OrsoEric/18650-Battery-Holder/Images/2024-06-14_17_49_IMG_20240614_174955.jpg

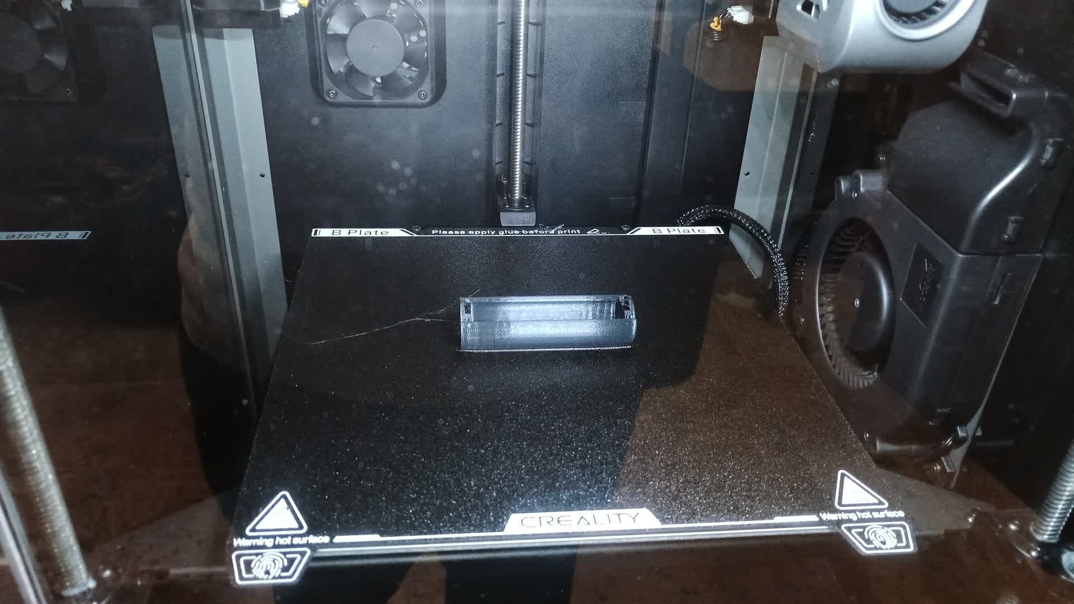
Images/2024-06-14_17_49_IMG_20240614_174955.jpg
