OrsoEric/18650-Battery-Holder/Images/2024-06-14_17_50_IMG_20240614_175002.jpg

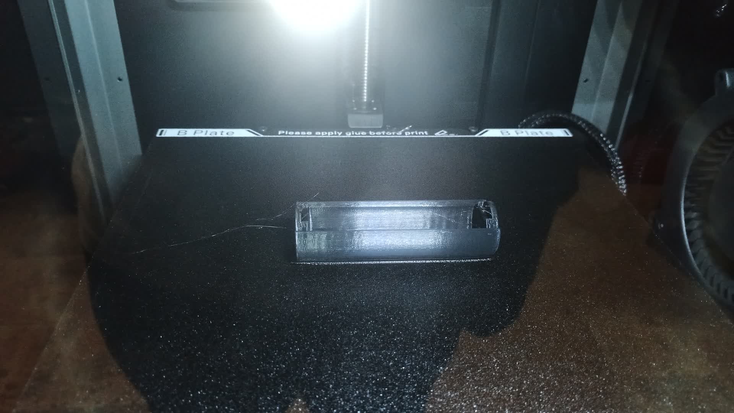
Images/2024-06-14_17_50_IMG_20240614_175002.jpg
