OrsoEric/18650-Battery-Holder/Images/2024-06-23_15_02_IMG_20240623_150227.jpg

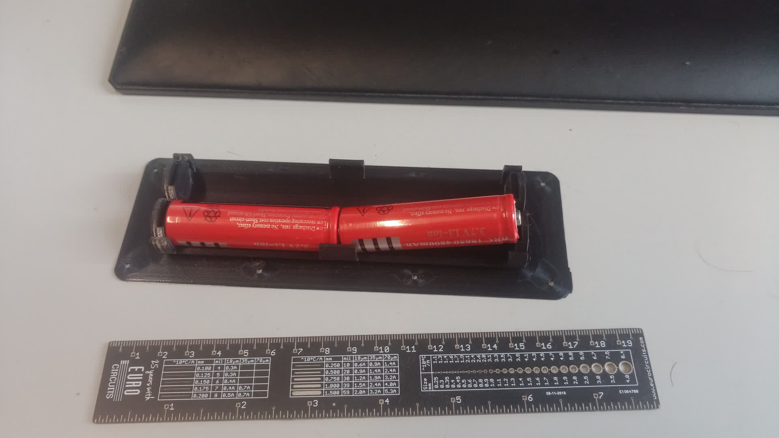
Images/2024-06-23_15_02_IMG_20240623_150227.jpg
