OrsoEric/18650-Battery-Holder/Images/2024-06-23_15_03_IMG_20240623_150332.jpg

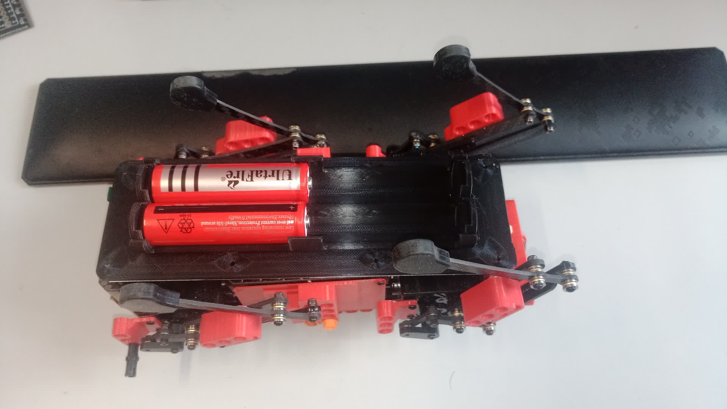
Images/2024-06-23_15_03_IMG_20240623_150332.jpg
