OrsoEric/18650-Battery-Holder/Images/2025-11-02_11_43_IMG_20251102_114355.jpg

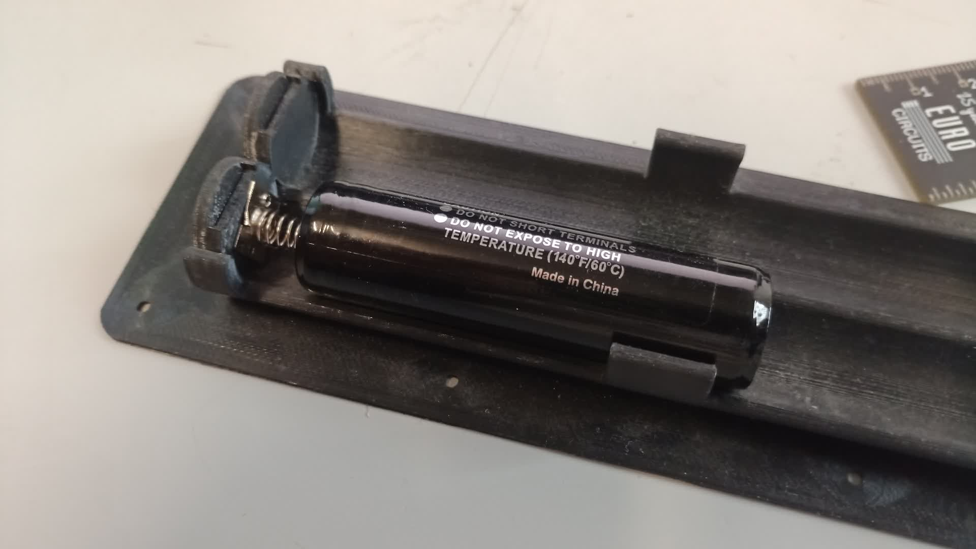
Images/2025-11-02_11_43_IMG_20251102_114355.jpg
