OrsoEric/18650-Battery-Holder/Images/2025-11-02_12_36_IMG_20251102_123628.jpg

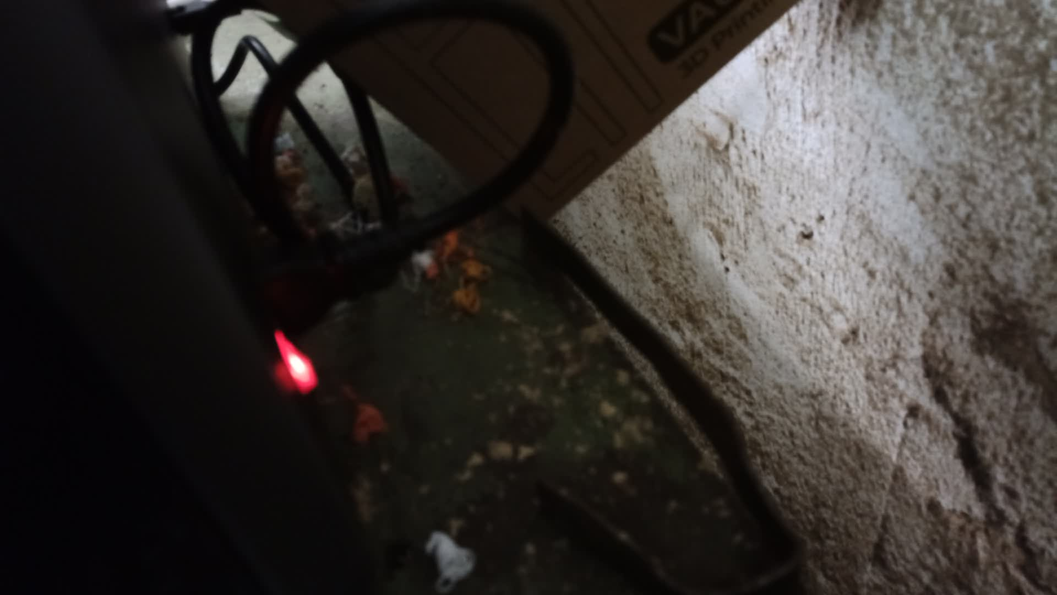
Images/2025-11-02_12_36_IMG_20251102_123628.jpg
