OrsoEric/18650-Battery-Holder/Images/2025-11-02_12_38_IMG_20251102_123847.jpg

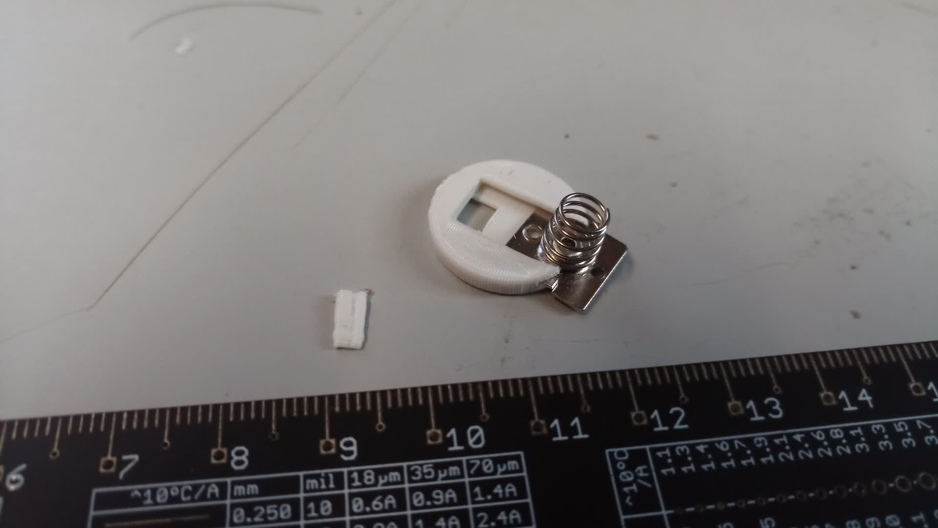
Images/2025-11-02_12_38_IMG_20251102_123847.jpg
