OrsoEric/18650-Battery-Holder/Images/2025-11-02_12_55_IMG_20251102_125501.jpg

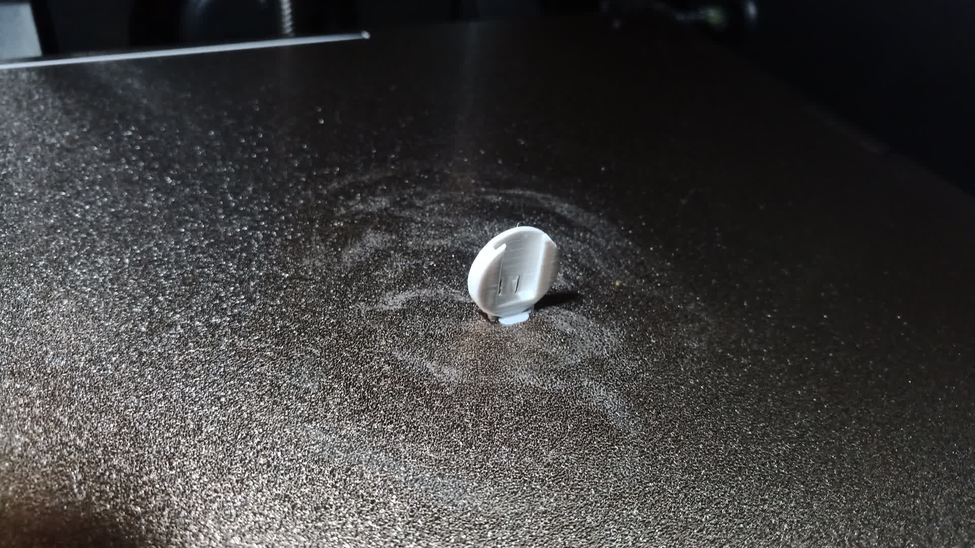
Images/2025-11-02_12_55_IMG_20251102_125501.jpg
