OrsoEric/18650-Battery-Holder/Images/2025-11-02_12_56_IMG_20251102_125633.jpg

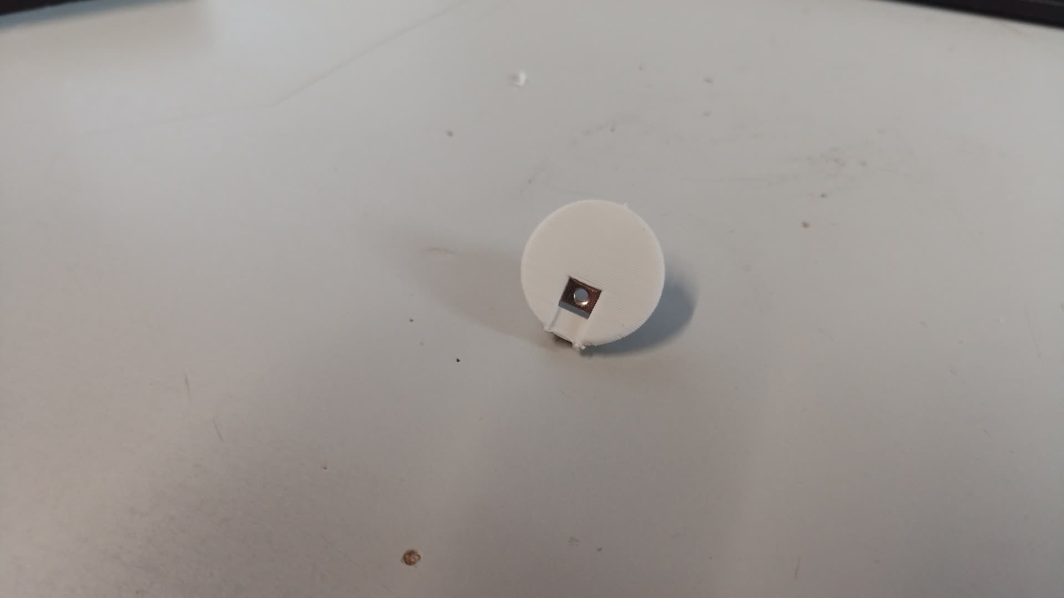
Images/2025-11-02_12_56_IMG_20251102_125633.jpg
