OrsoEric/18650-Battery-Holder/Images/2025-11-02_13_31_IMG_20251102_133140.jpg

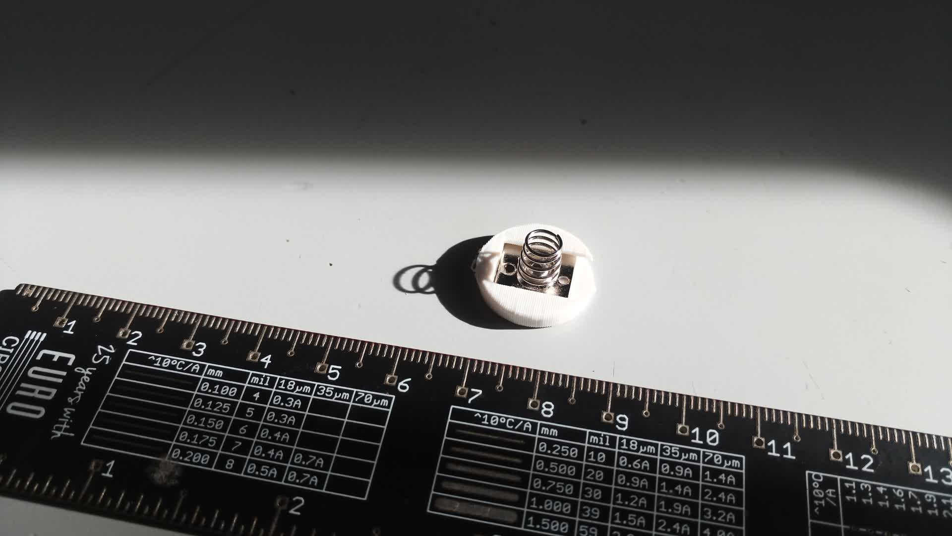
Images/2025-11-02_13_31_IMG_20251102_133140.jpg
