OrsoEric/18650-Battery-Holder/Images/2025-11-02_16_00_IMG_20251102_160055.jpg

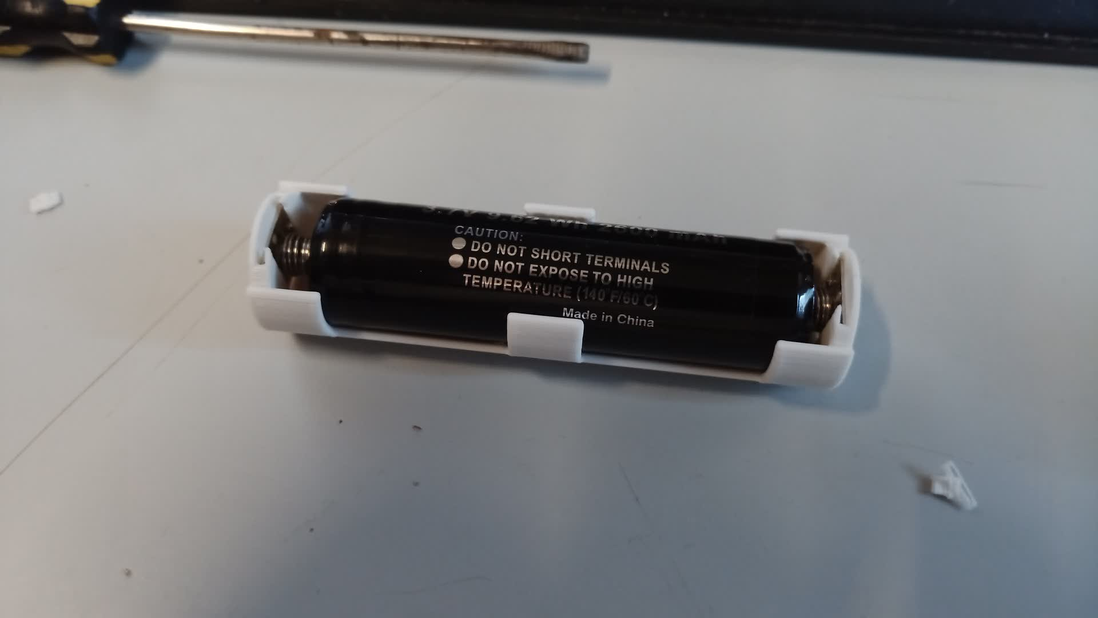
Images/2025-11-02_16_00_IMG_20251102_160055.jpg
