OrsoEric/18650-Battery-Holder/Images/2025-11-02_16_02_IMG_20251102_160204.jpg

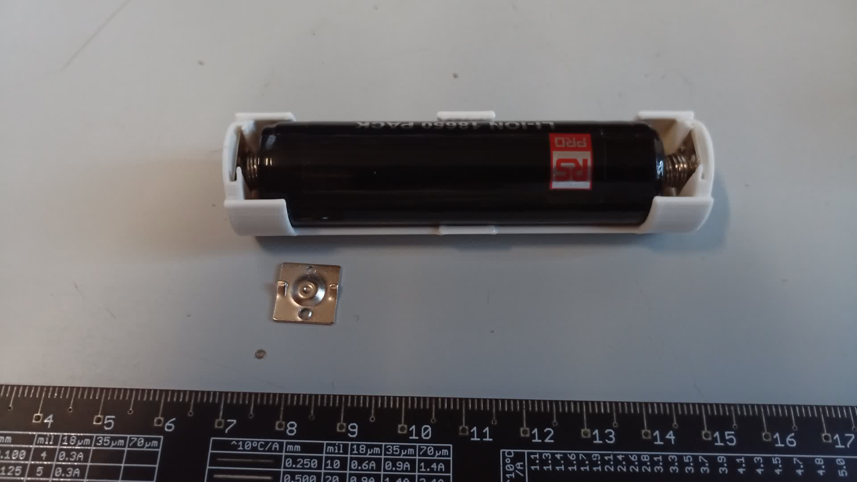
Images/2025-11-02_16_02_IMG_20251102_160204.jpg
