OrsoEric/18650-Battery-Holder/Images/2025-11-02_19_18_IMG_20251102_191812.jpg

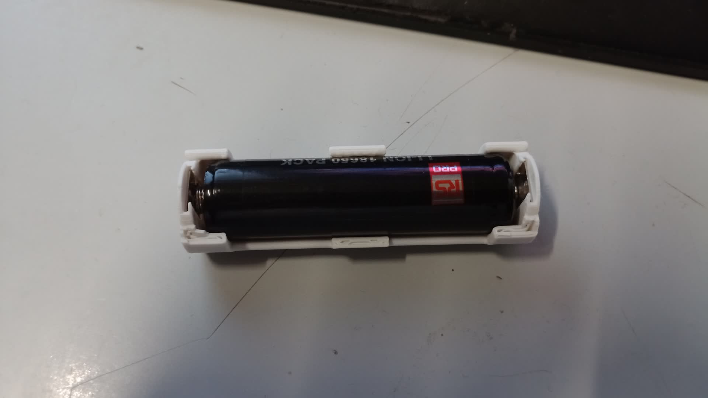
Images/2025-11-02_19_18_IMG_20251102_191812.jpg
