OrsoEric/18650-Battery-Holder/Images/2025-11-06_12_01_IMG_20251106_120114.jpg

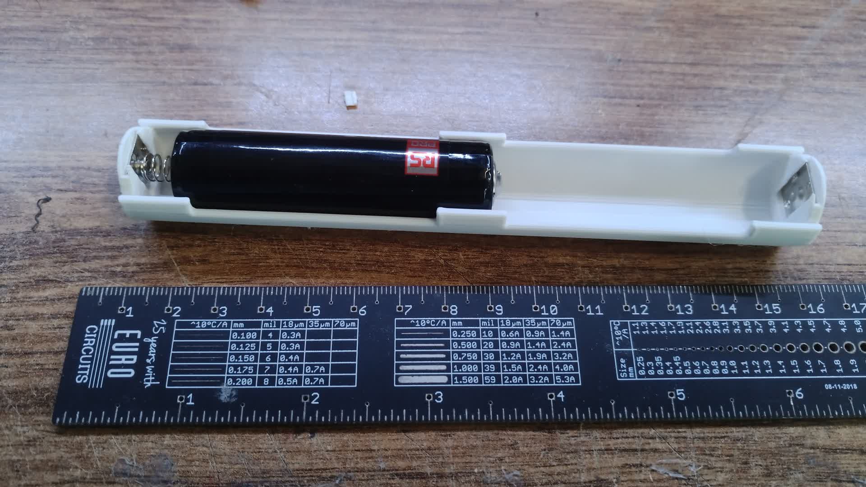
Images/2025-11-06_12_01_IMG_20251106_120114.jpg
