OrsoEric/18650-Battery-Holder/Images/battery-18650.scad - OpenSCAD 2024-05-14 17_54_38.png

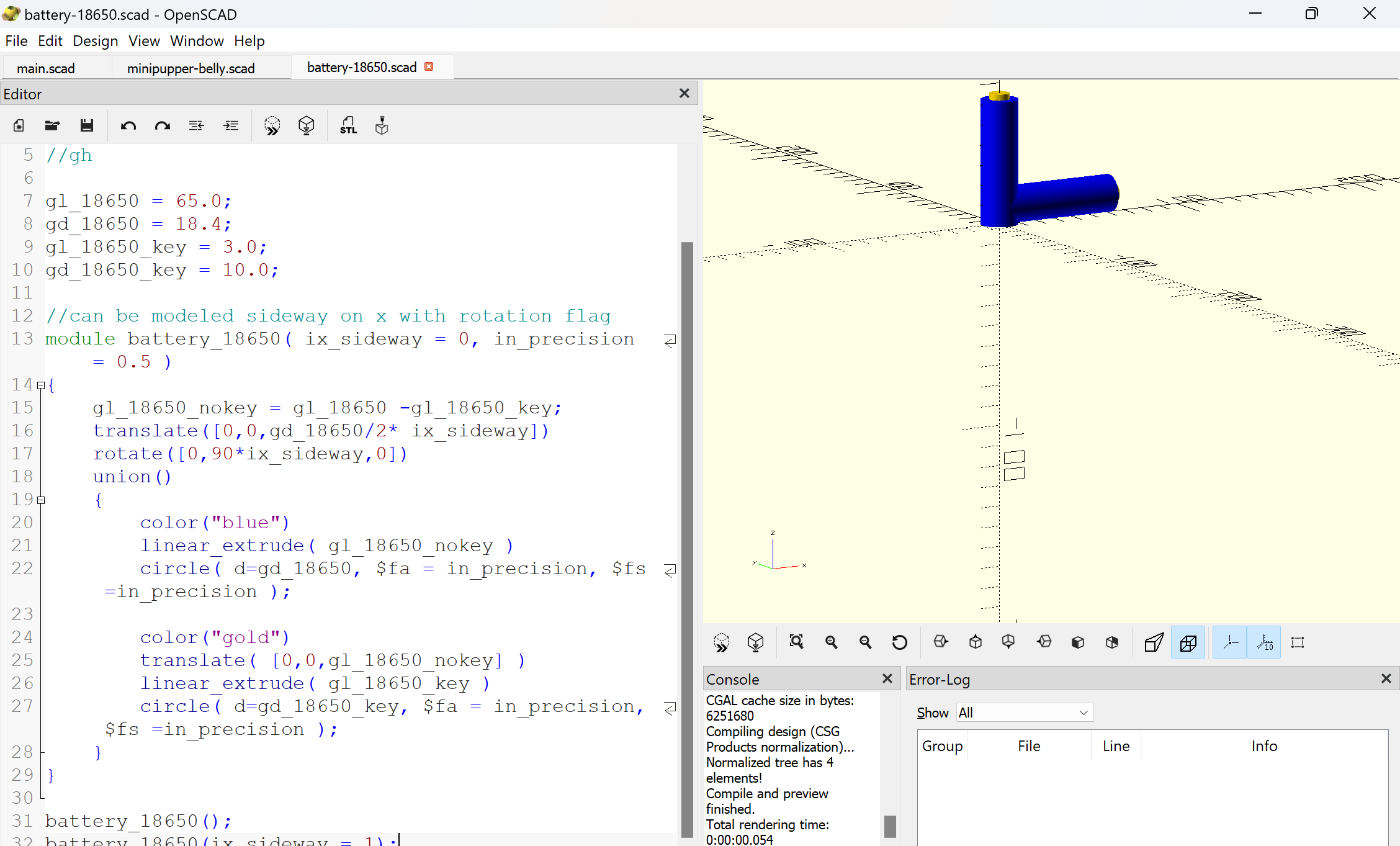
Images/battery-18650.scad - OpenSCAD 2024-05-14 17_54_38.png
