OrsoEric/18650-Battery-Holder/Images/battery-18650.scad - OpenSCAD 2024-05-14 18_05_54.png

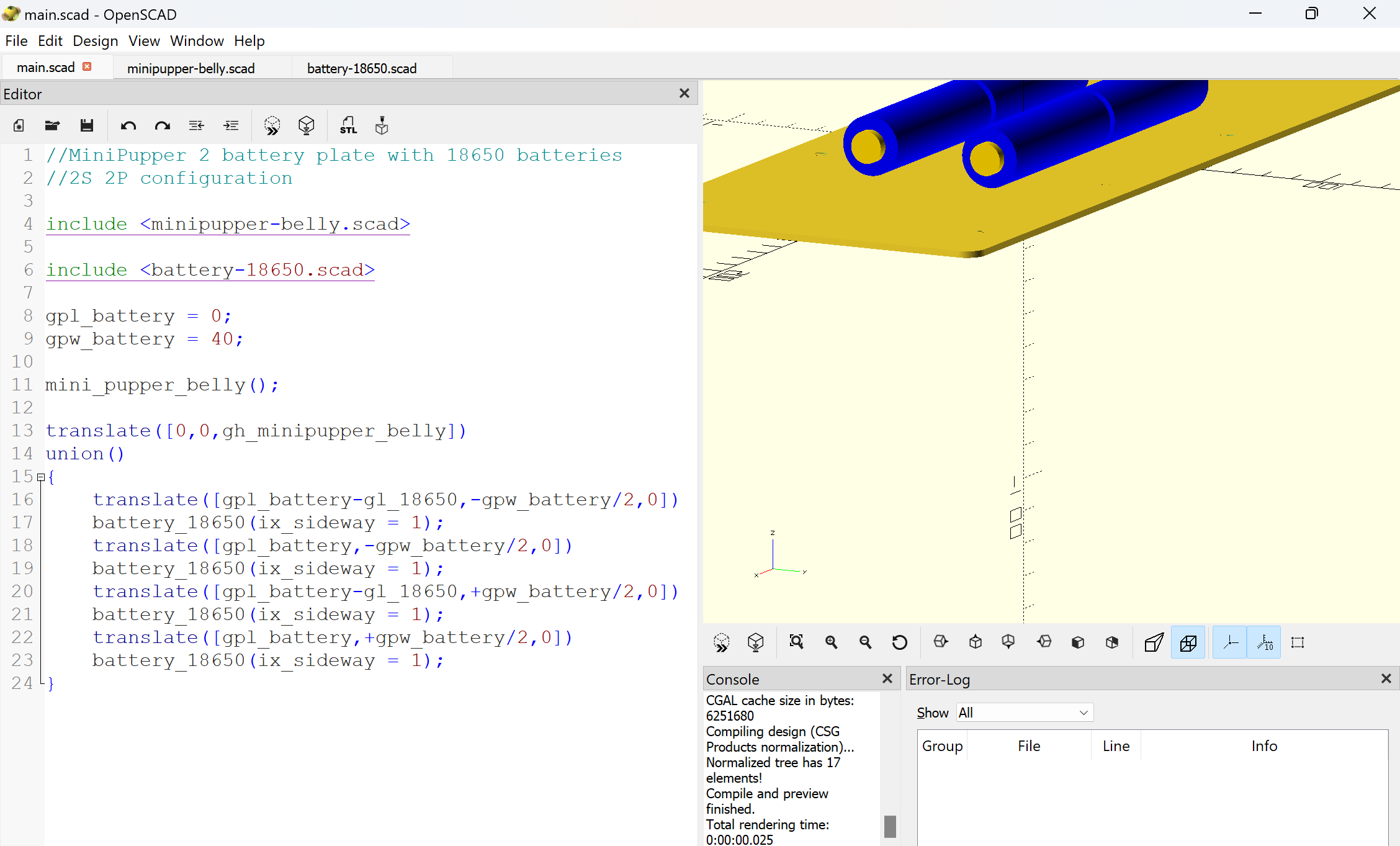
Images/battery-18650.scad - OpenSCAD 2024-05-14 18_05_54.png
