OrsoEric/18650-Battery-Holder/Images/battery-18650.scad - OpenSCAD 2024-06-11 18_25_42.png

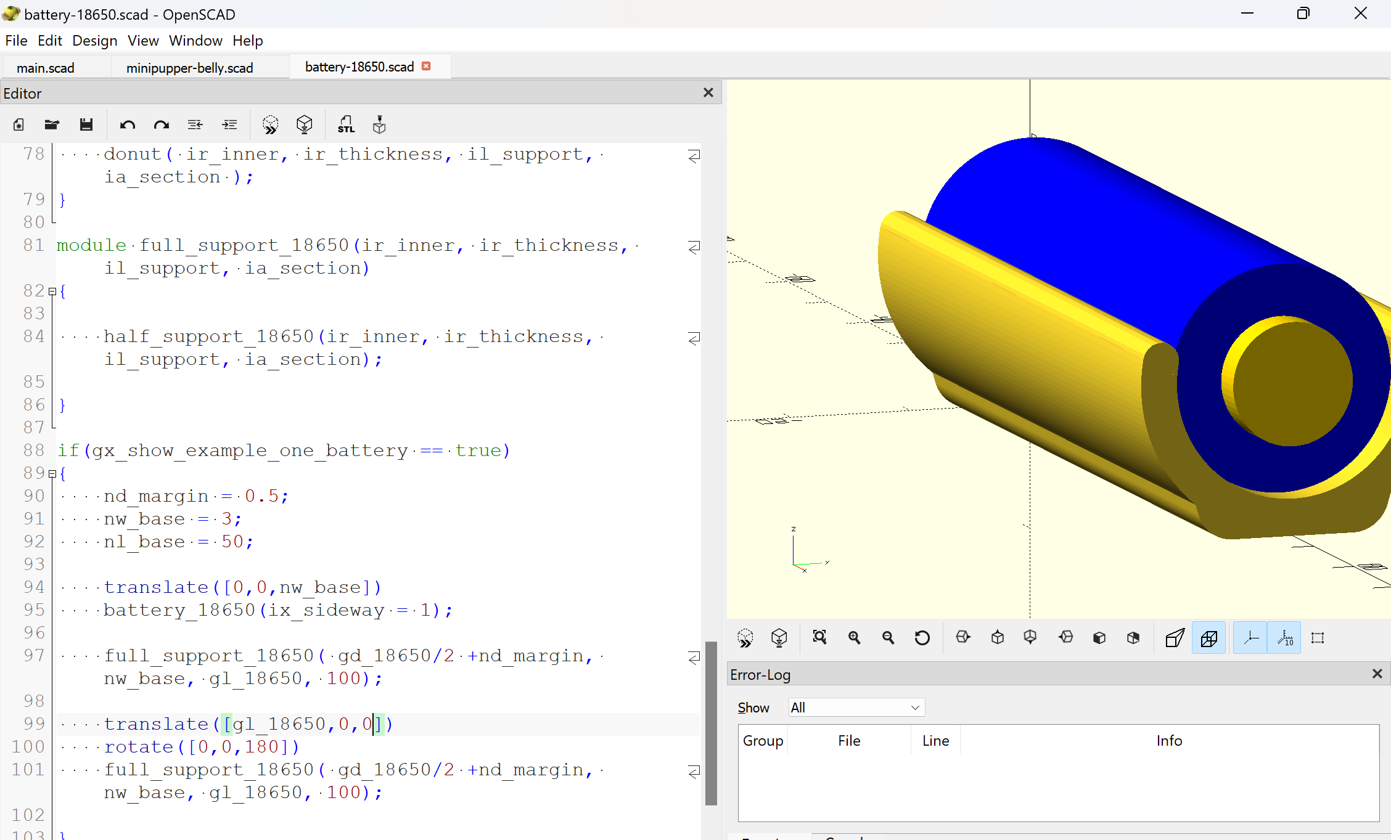
Images/battery-18650.scad - OpenSCAD 2024-06-11 18_25_42.png
