OrsoEric/18650-Battery-Holder/Images/battery-18650.scad - OpenSCAD 2024-06-13 17_30_02.png

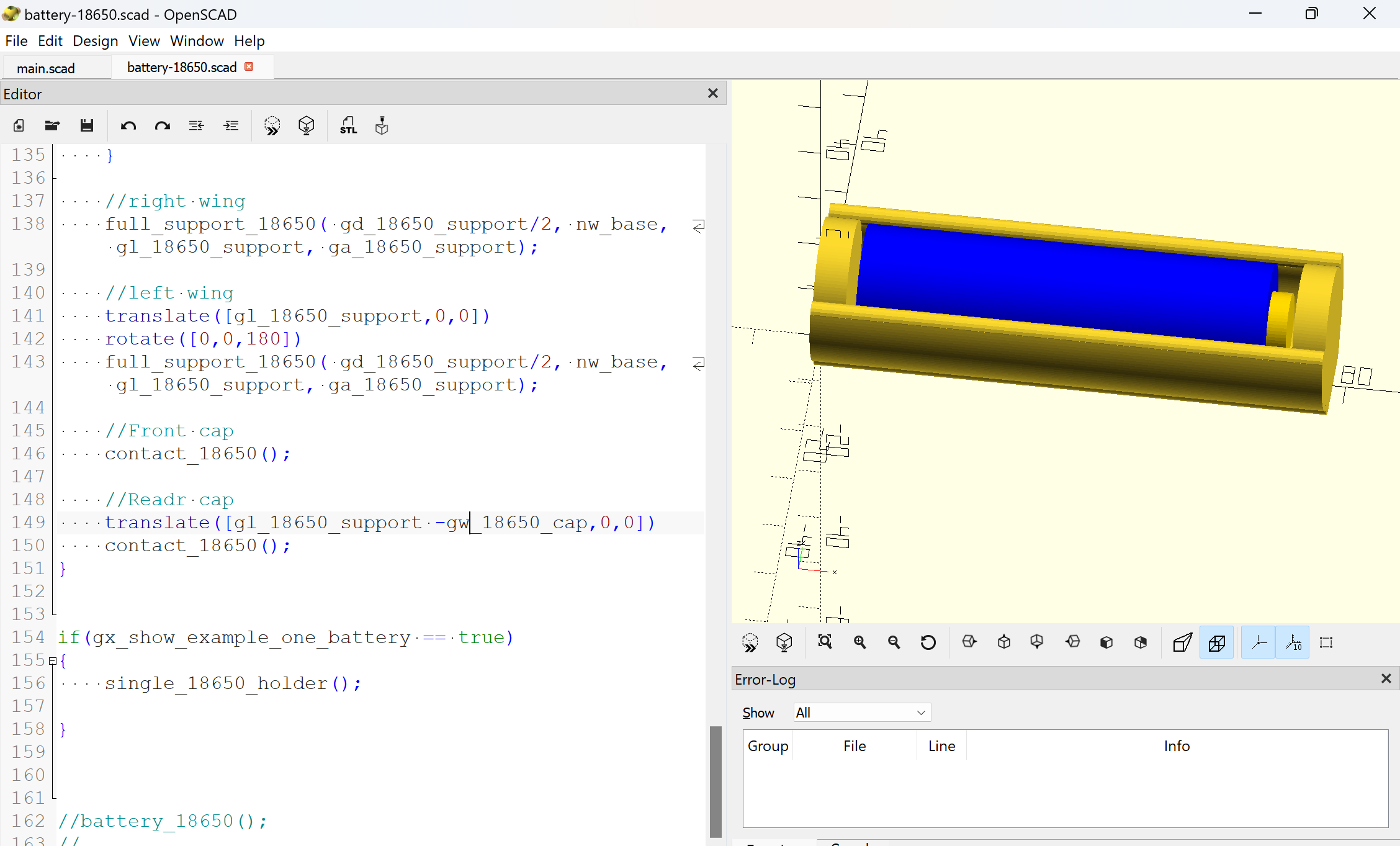
Images/battery-18650.scad - OpenSCAD 2024-06-13 17_30_02.png
