OrsoEric/18650-Battery-Holder/Images/battery-18650.scad - OpenSCAD 2024-06-13 18_05_08.png

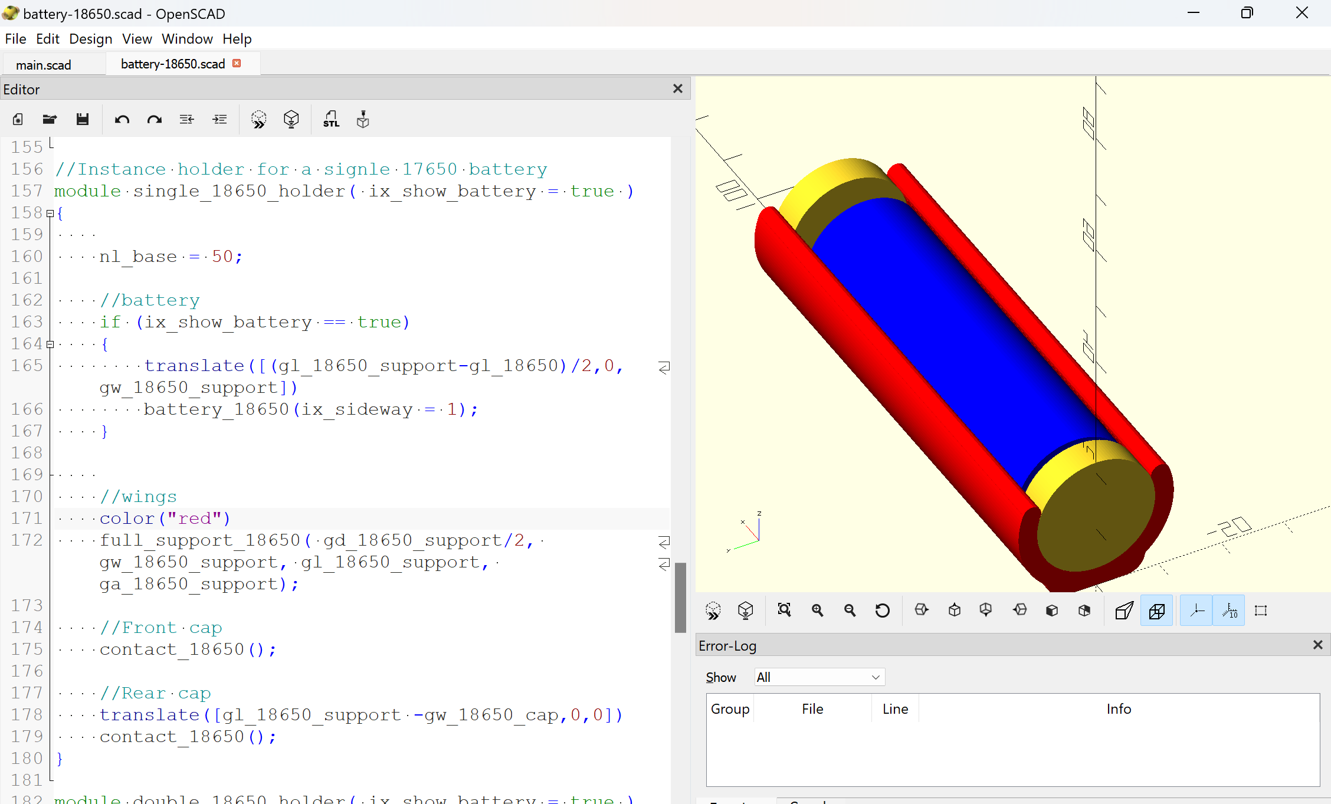
Images/battery-18650.scad - OpenSCAD 2024-06-13 18_05_08.png
