OrsoEric/18650-Battery-Holder/Images/battery-18650.scad - OpenSCAD 2024-06-20 17_51_42.png

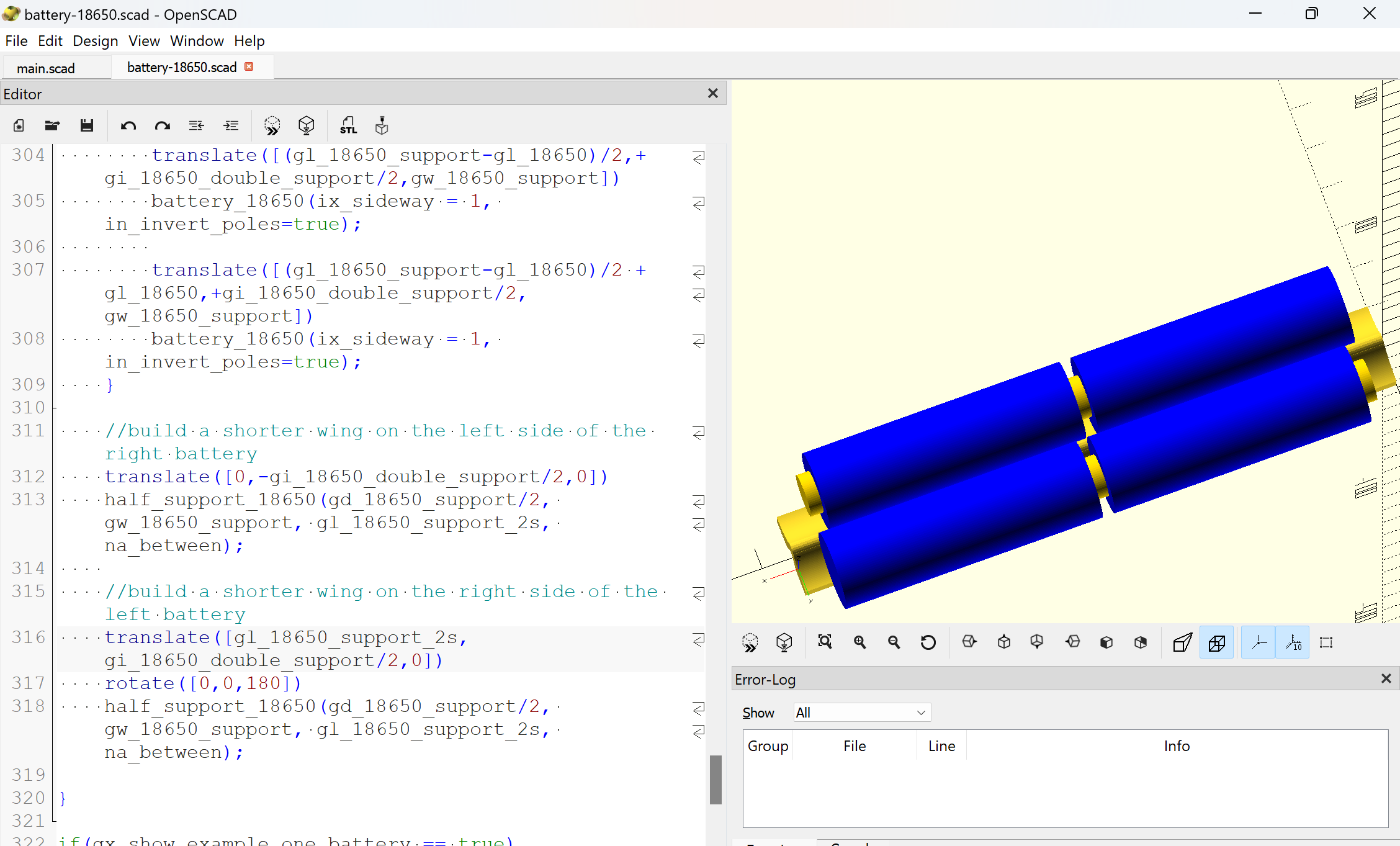
Images/battery-18650.scad - OpenSCAD 2024-06-20 17_51_42.png
