OrsoEric/18650-Battery-Holder/Images/battery-18650.scad - OpenSCAD 2024-06-20 18_07_56.png

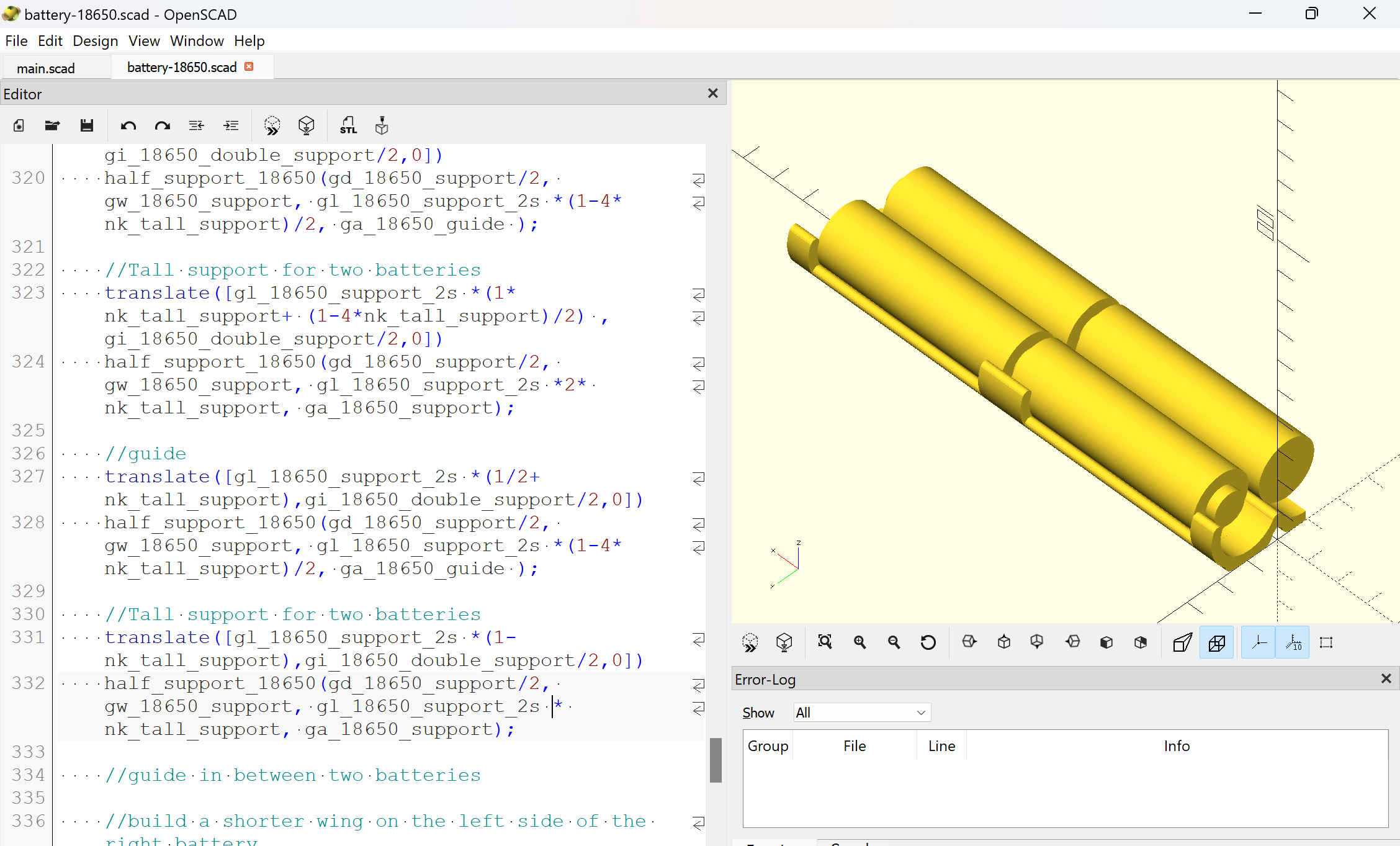
Images/battery-18650.scad - OpenSCAD 2024-06-20 18_07_56.png
