OrsoEric/18650-Battery-Holder/Images/battery-18650.scad_ - OpenSCAD 2024-06-13 18_03_09.png

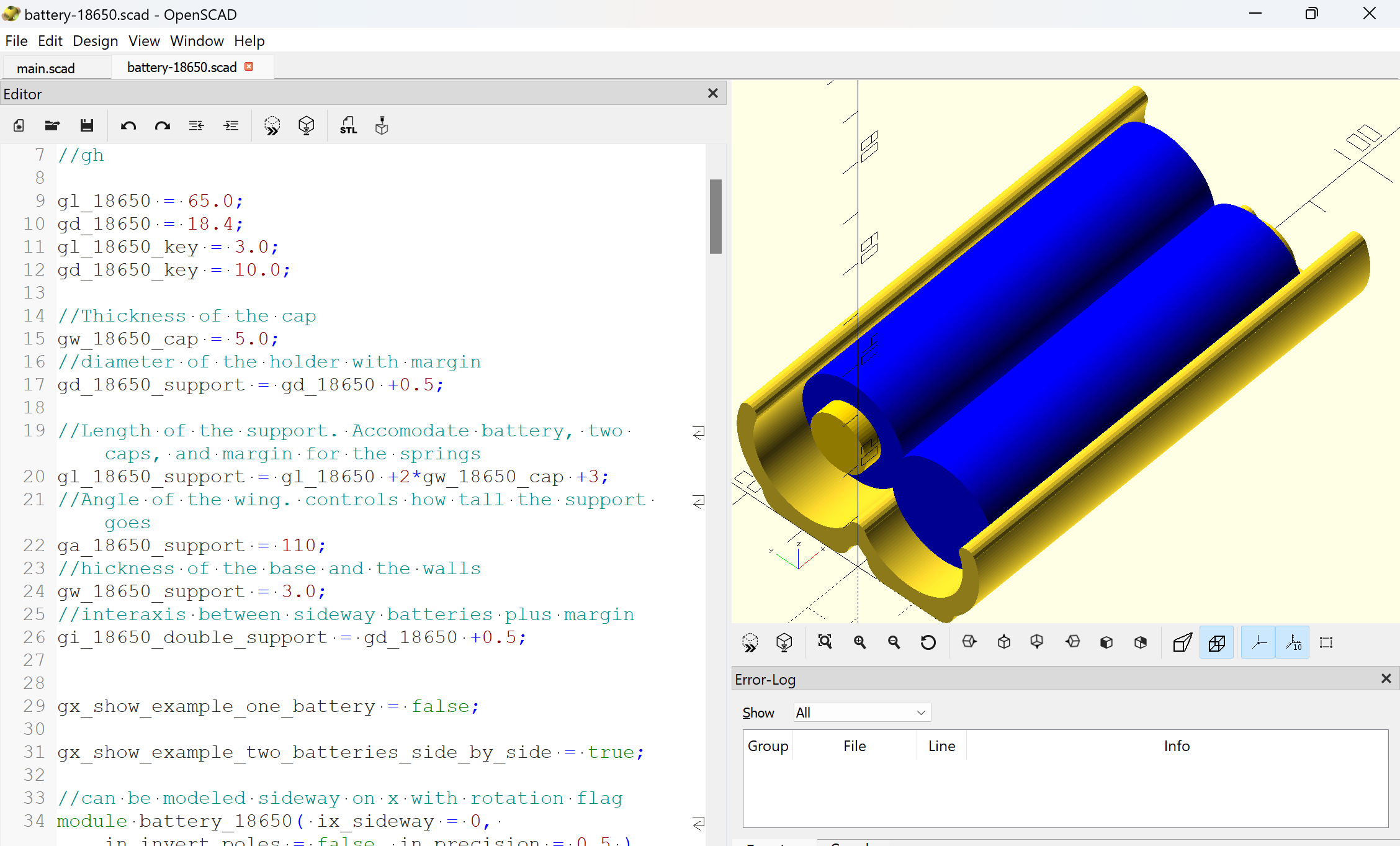
Images/battery-18650.scad_ - OpenSCAD 2024-06-13 18_03_09.png
