OrsoEric/18650-Battery-Holder/Images/IMG_20251102_105544.jpg

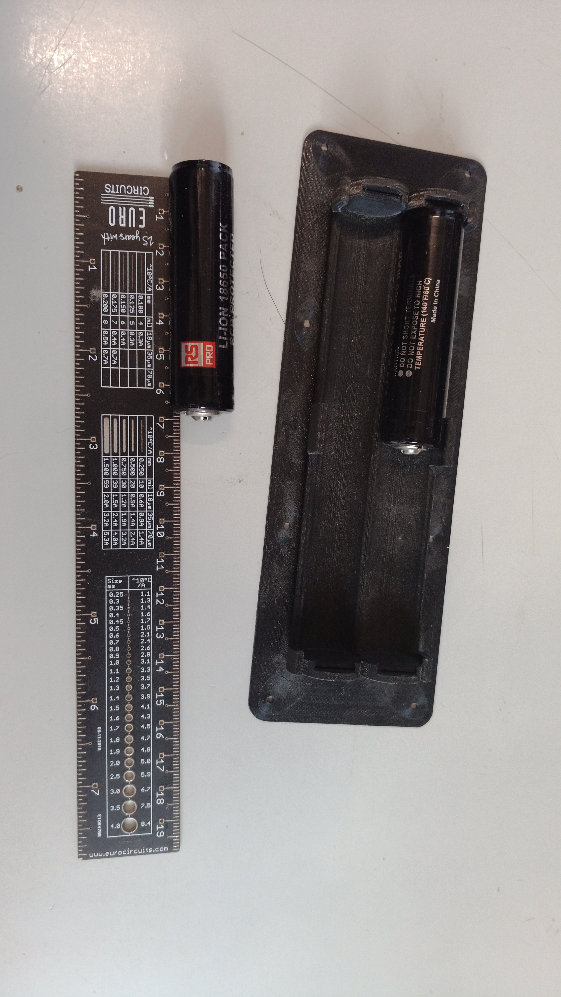
Images/IMG_20251102_105544.jpg
