OrsoEric/18650-Battery-Holder/Images/main.scad - OpenSCAD 2024-05-26 15_30_59.png

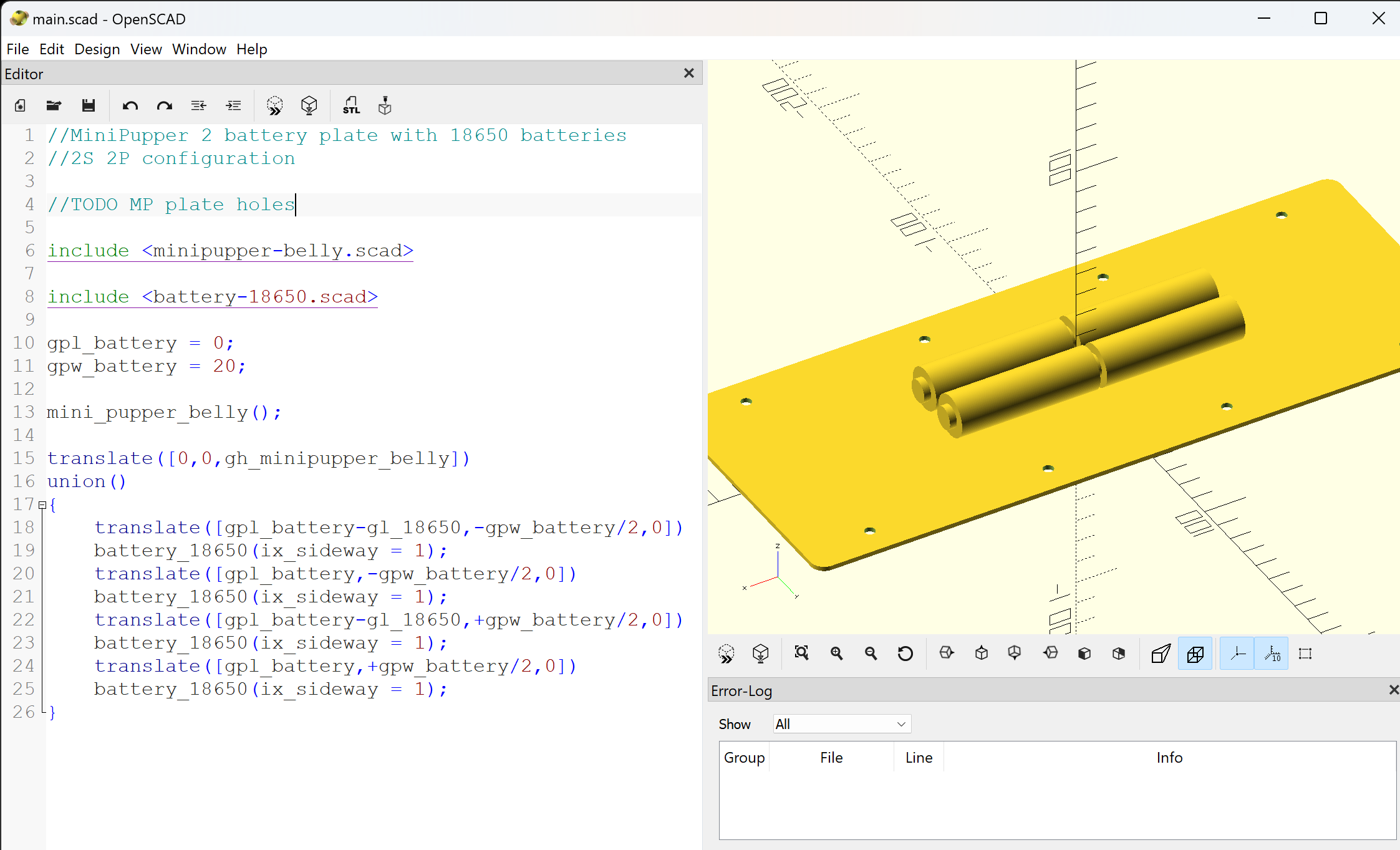
Images/main.scad - OpenSCAD 2024-05-26 15_30_59.png
