OrsoEric/18650-Battery-Holder/Images/main.scad - OpenSCAD 2024-06-11 18_01_33.png

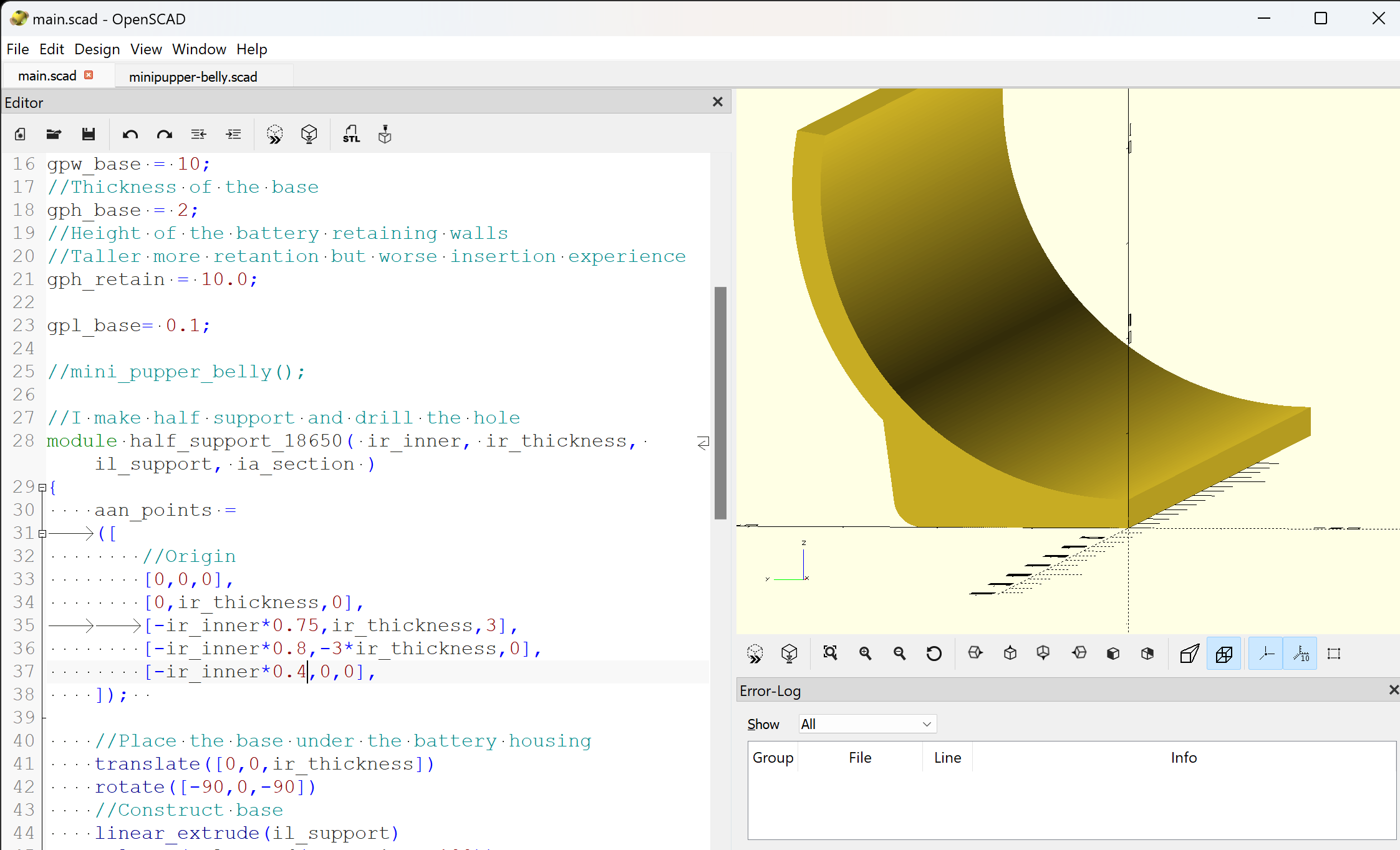
Images/main.scad - OpenSCAD 2024-06-11 18_01_33.png
