OrsoEric/18650-Battery-Holder/Images/main.scad - OpenSCAD 2024-06-20 18_17_02.png

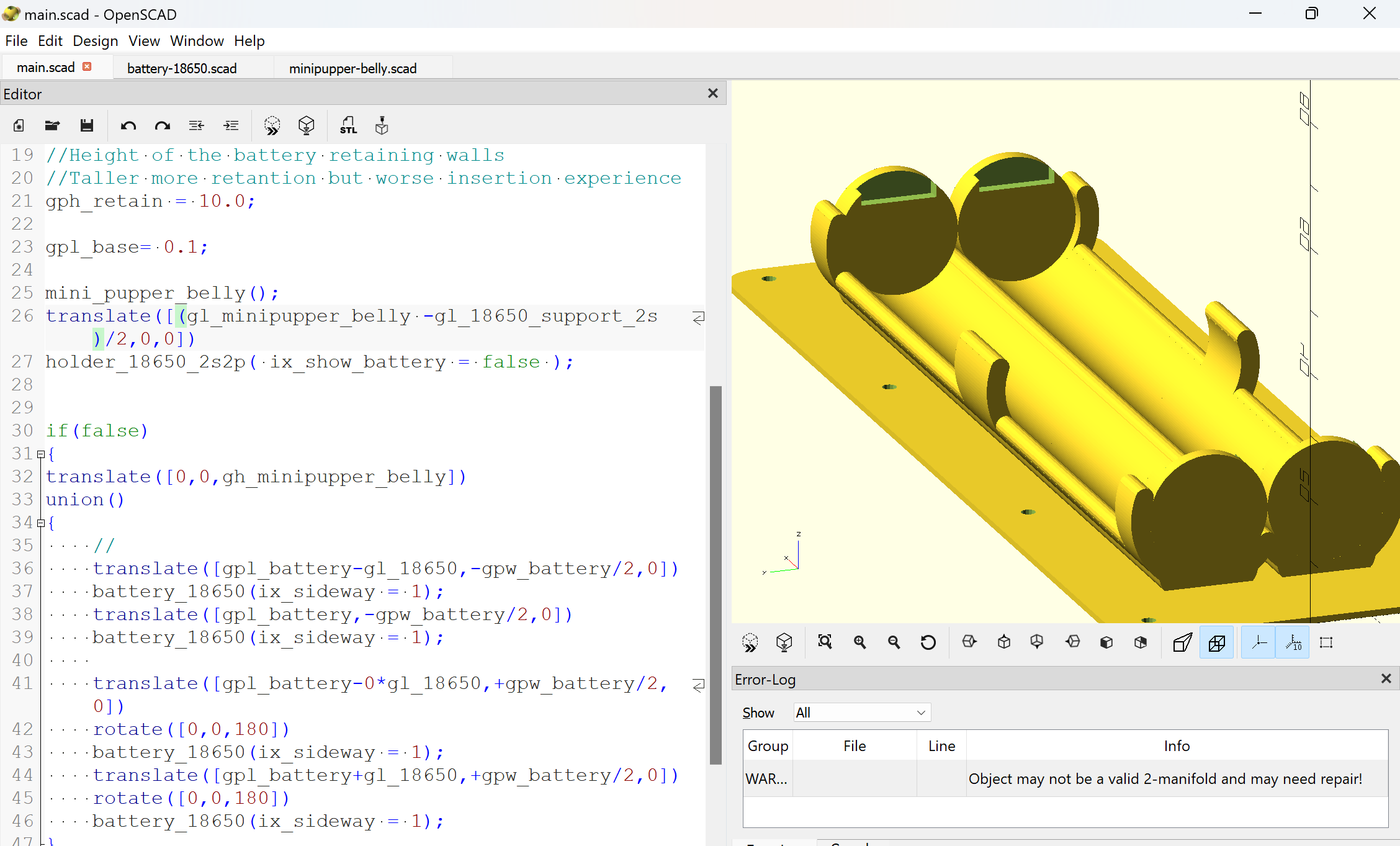
Images/main.scad - OpenSCAD 2024-06-20 18_17_02.png
