OrsoEric/18650-Battery-Holder/Images/main.scad_ - OpenSCAD 2024-06-11 18_10_45.png

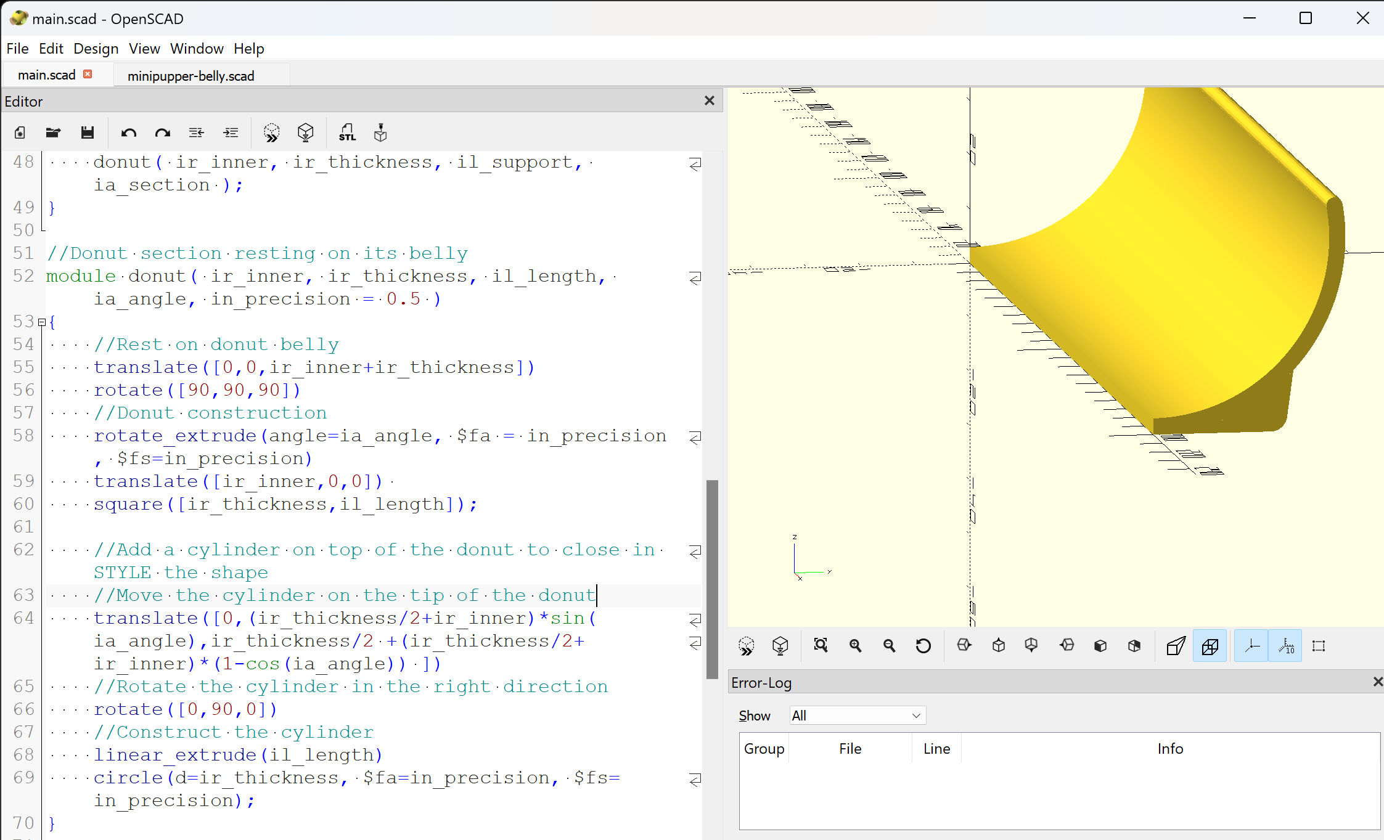
Images/main.scad_ - OpenSCAD 2024-06-11 18_10_45.png
