OrsoEric/18650-Battery-Holder/Images/Screenshot 2025-09-19 072542.png

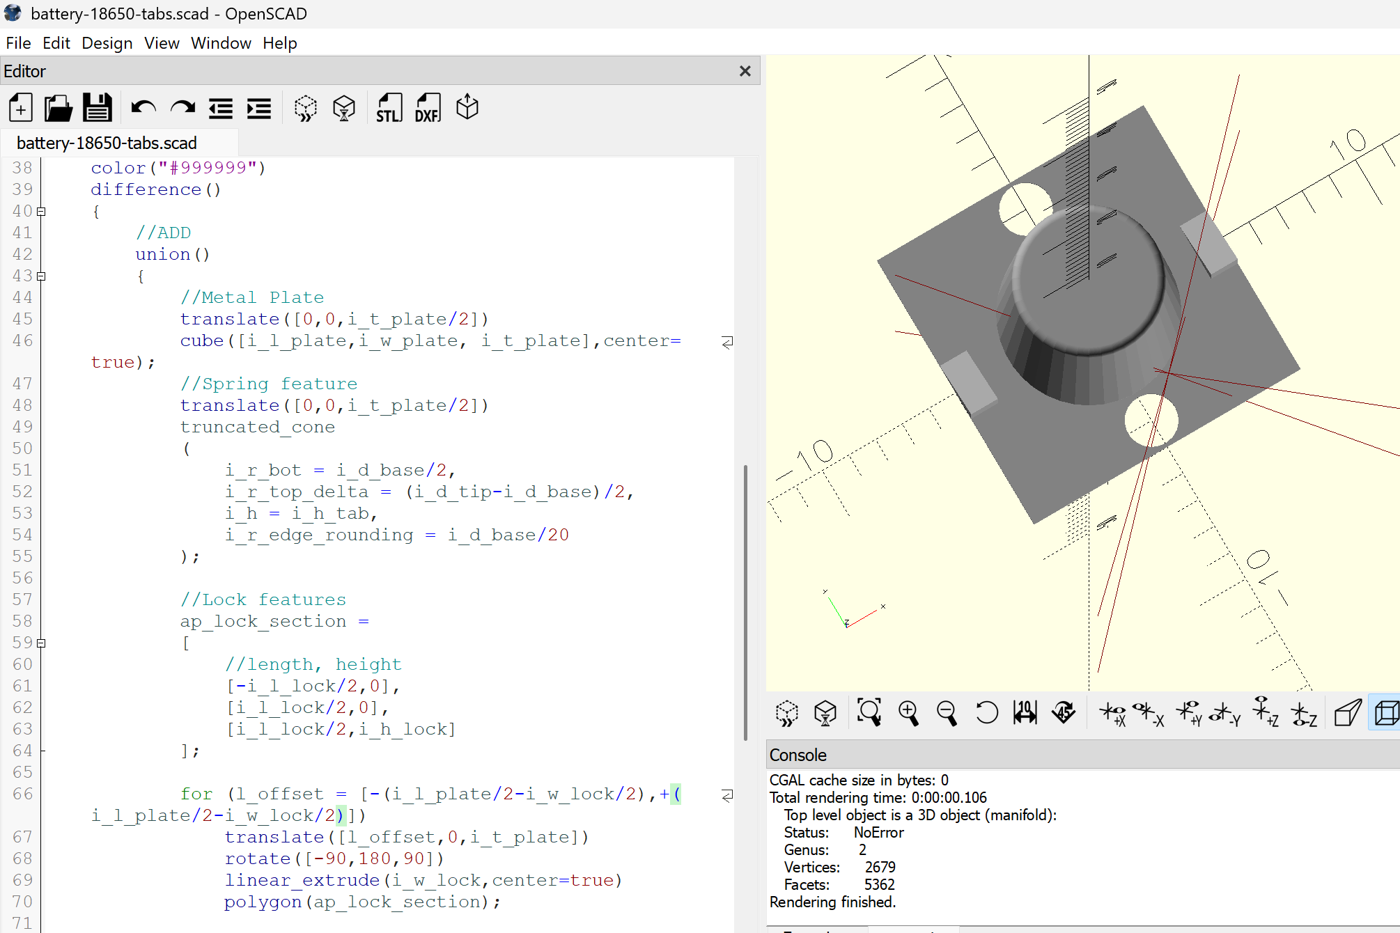
Images/Screenshot 2025-09-19 072542.png
