OrsoEric/18650-Battery-Holder/Images/Screenshot 2025-11-02 121937.png

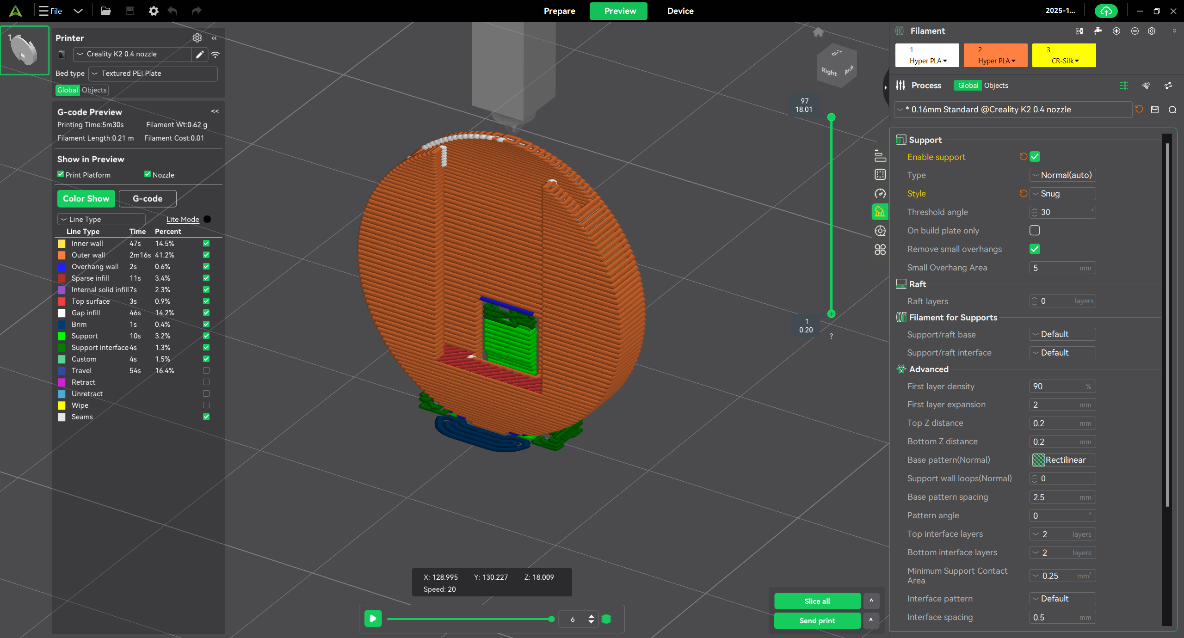
Images/Screenshot 2025-11-02 121937.png
