OrsoEric/18650-Battery-Holder/Images/Screenshot 2025-11-02 135137.png

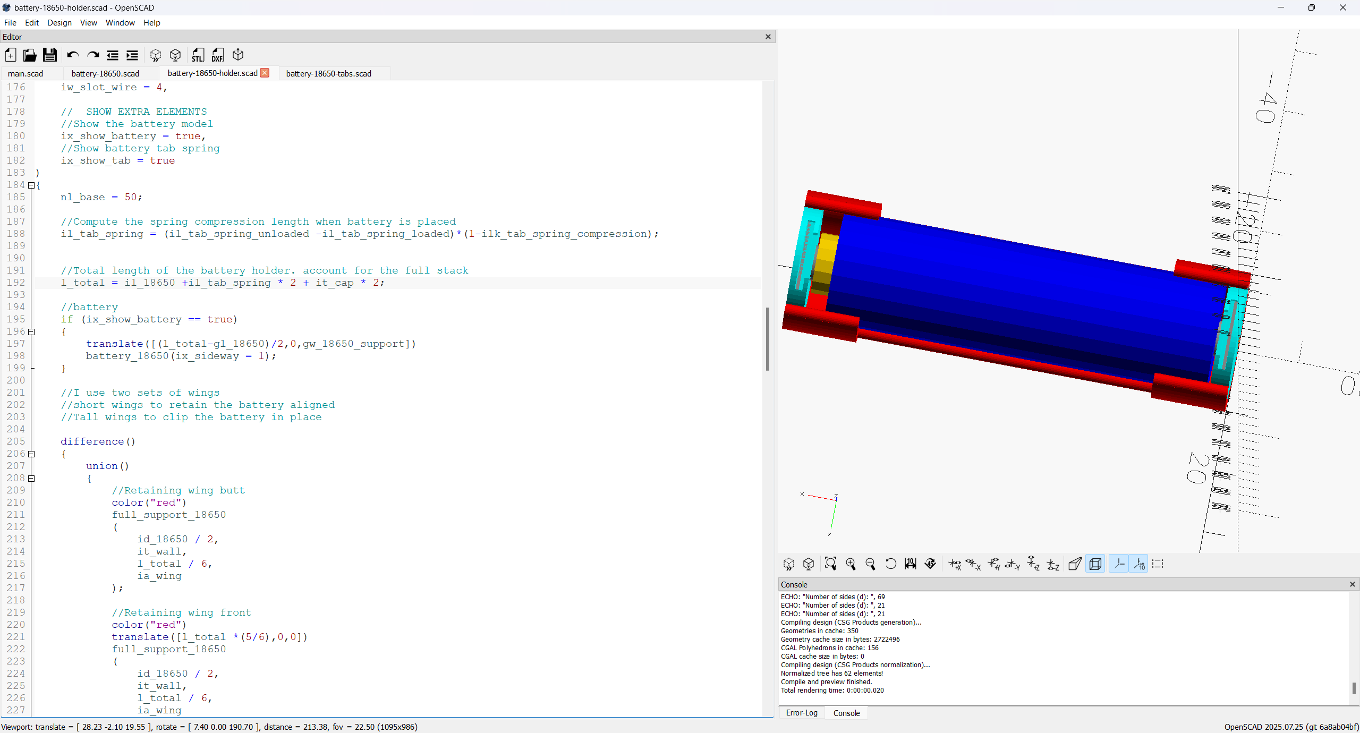
Images/Screenshot 2025-11-02 135137.png
