OrsoEric/18650-Battery-Holder/Images/Screenshot 2025-11-02 162125.png

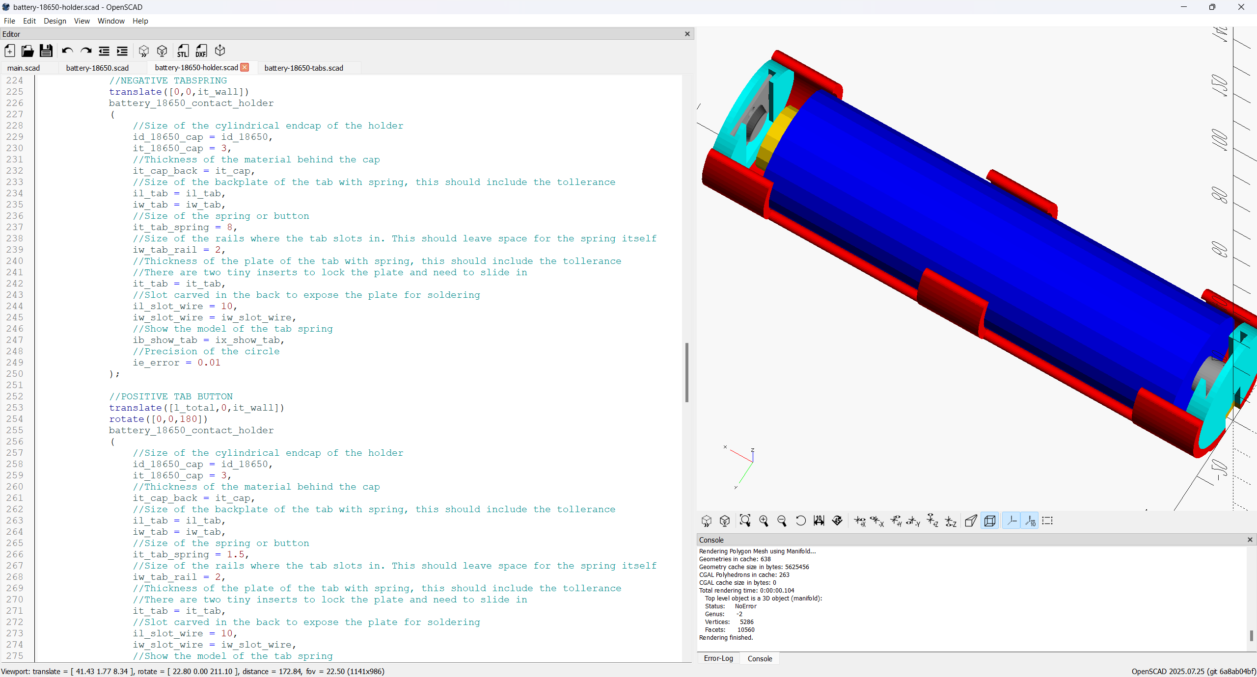
Images/Screenshot 2025-11-02 162125.png
