OrsoEric/18650-Battery-Holder/Images/Screenshot 2025-11-02 164821.png

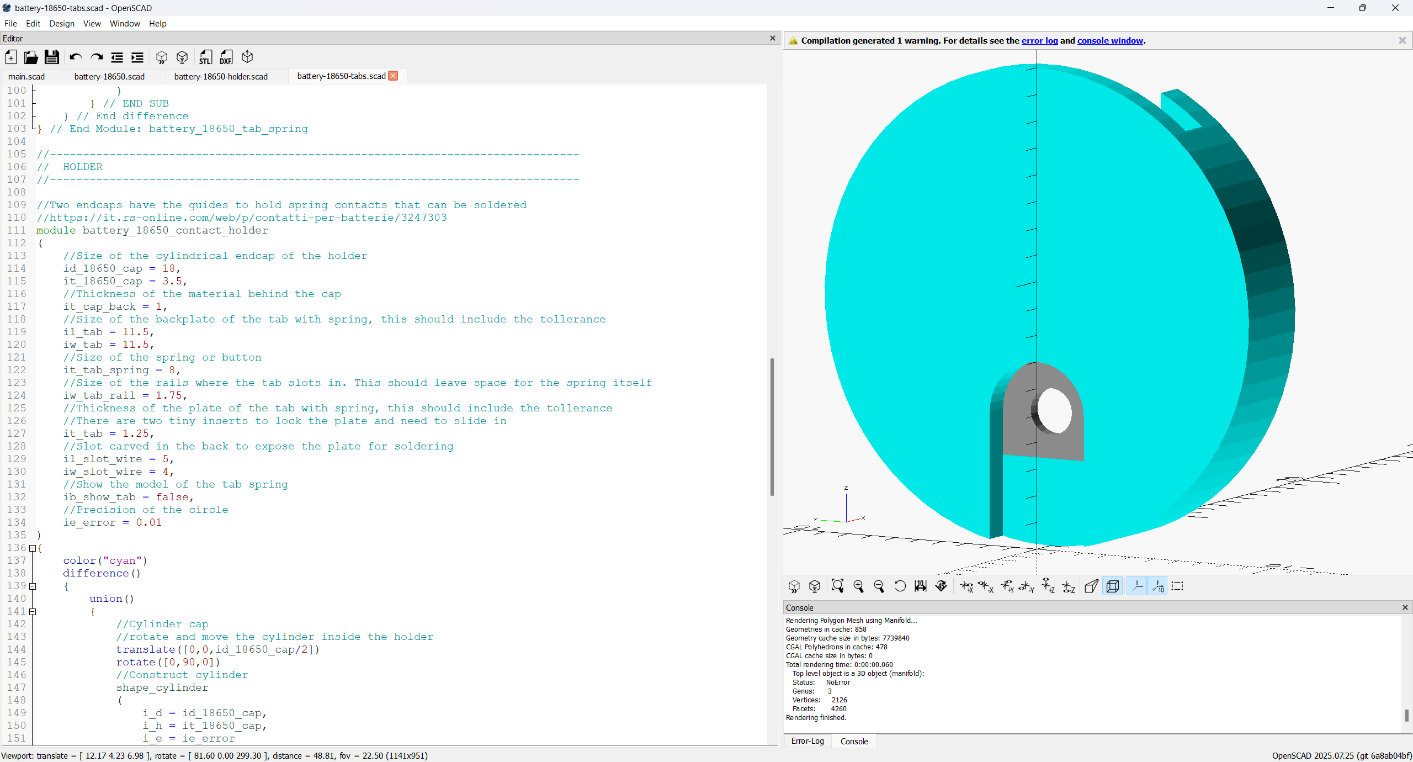
Images/Screenshot 2025-11-02 164821.png
