OrsoEric/18650-Battery-Holder/Images/Screenshot 2025-11-06 112357.png

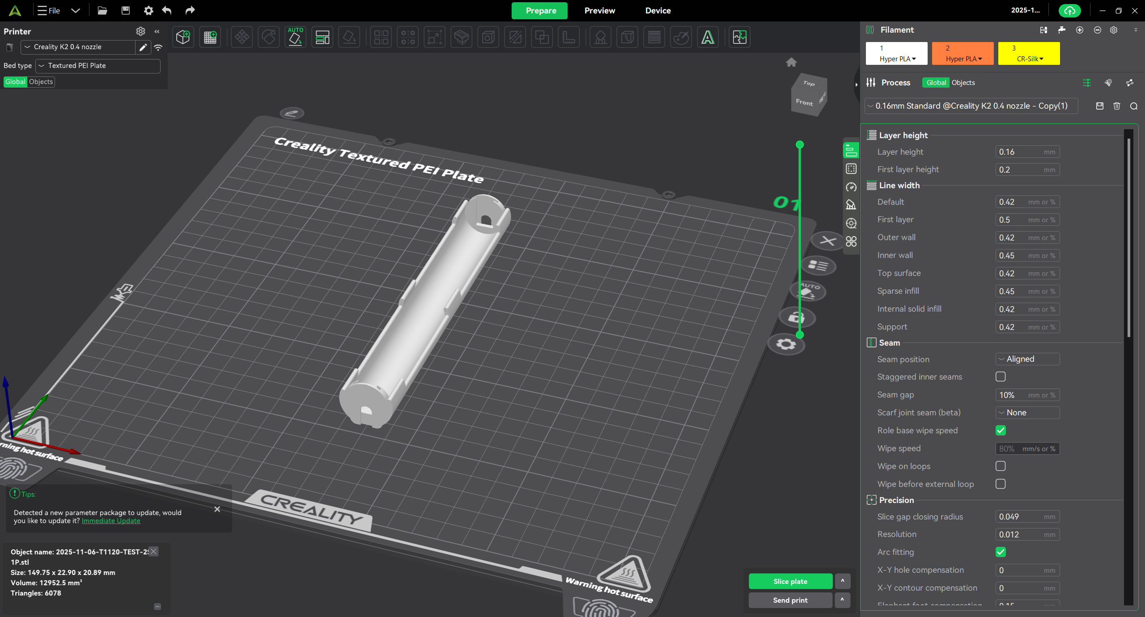
Images/Screenshot 2025-11-06 112357.png
