OrsoEric/18650-Battery-Holder/Images/Screenshot 2025-11-06 122348.png

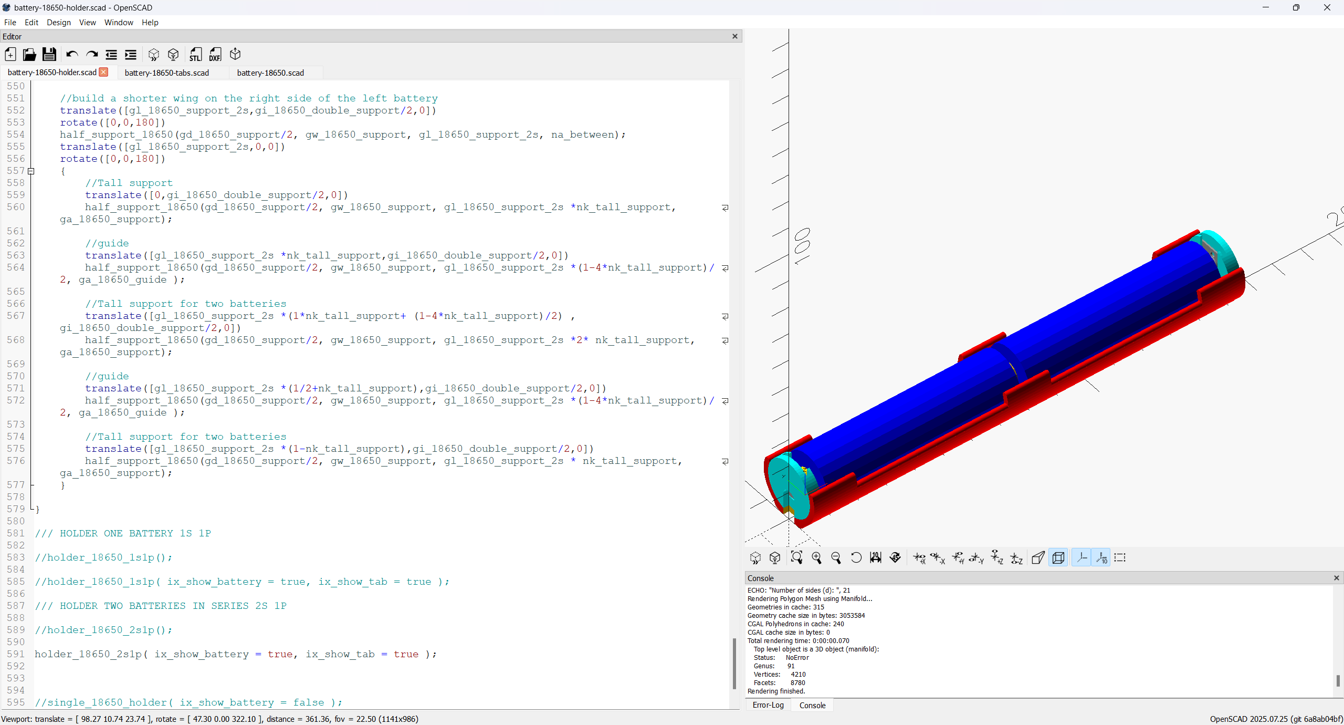
Images/Screenshot 2025-11-06 122348.png
