OrsoEric/18650-Battery-Holder/Images/Creality Print 2024-06-20 18_18_58.png

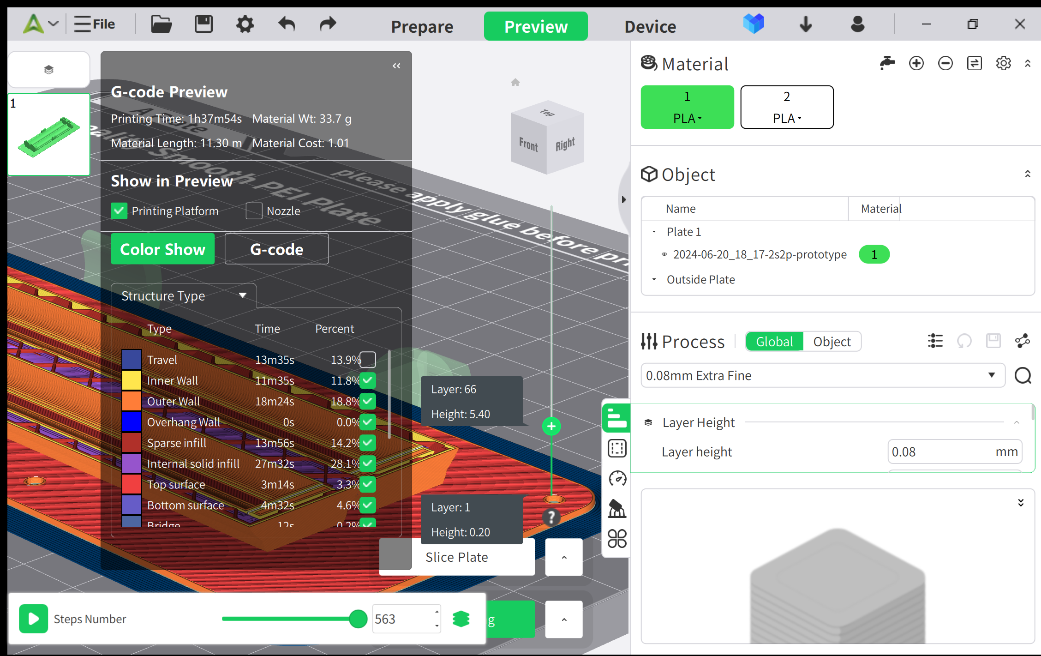
Images/Creality Print 2024-06-20 18_18_58.png
